BoujeeEnjinia1701/gridbench/cad/drawings/GBN-DWG-001.pdf

CONCEPT, NOT FOR FABRICATION | GridBench · github.com/BoujeeEnjinia1701/gridbench

FRONT VIEW
Scale 1:20; looking at the front (along +Y)

TOP VIEW
Scale 1:20; looking down (along -Z)

RIGHT VIEW
Scale 1:20; looking at the right side (along -X)

1200

600 1262

DETAIL A: TILE
Top view, scale 1:5

DETAIL A NOTES
Holes continue the field grid 4 fixing holes, 7 mm, C'bore 11 Tile 12.7 thick on 5.3 packers

FLOOR

1,090 FEET

14 BALLAST, 2 SLABS

825 | 300

6 PRECISION TILE, FLUSH

4 PLYWOOD FIELD, 25 GRID

122 LIGHT-DUTY RINGS (RED)

12.5

25

9 x 8 H7, 100 PITCH

144 x M6

ISOMETRIC VIEW
Not to scale; worktop holes shown as a representative patch; seen from the front right and above, about 30 deg elevation

MAIN DIMENSIONS AND INTERFACES (MM)
Worktop 1,200 x 600 x 18 birch ply, top at 900 ±15
Grid 25 pitch, first hole 12.5 from each edge; 1,152 positions
Field: 756 x 6.6 plain; 252 M6 on the 50 sub-grid: 130 tee nuts from below, 122 screw-in over frame Tile 300 x 300 x 12.7, left edge 825 from the worktop's left edge
Feet at 1,090 x 490 centers, rubber pads, in M10 T-nuts; legs 70 square
Aprons 45 x 120; cross rails 45 x 70 at X -300, 0, 247.5, 502.5
Clamp 1.6 N m max; 0.92 N m at the 122 red-ringed light-duty positions; round + diamond pin Aprons and low rails butt between the legs: 2 M8 bolts and cross dowels per end
Worktop on 9 steel angle brackets; tile on 4 M6 x 20 screws into rail inserts
Ballast 2 x 12.9 kg slabs on a shelf screwed to the low rails (8 screws)
Third-angle; front view from -Y; origin at worktop center
REV | DESCRIPTION | DATE | BY
P1 | Preliminary GA for TRL 3 (from cad/src/model.py) | 2026-09-25 | AC
P2 | Recommendations accepted (DDR-002): 45 x 120 aprons, tee nuts, rubber feet | 2026-09-25 | AC
P3 | Layout and labels tidied | 2026-09-25 | AC
P4 | Design for construction (DDR-003): bolted joints, brackets, tile fixing | 2026-10-01 | AC
P5 | Light-duty rings at the screw-in positions; shelf screwed to the low rails | 2026-10-02 | AC
GRIDBENCH | github.com/BoujeeEnjinia1701/gridbench

## General arrangement

DRAWING NO.
GBN-DWG-001

REV
P5

SHEET
1 of 1

SIZE

## ANSI B

SCALE
1:20

UNITS
mm
PROJECTION | DATE
2026-10-02

DRAWN
Amish Chadha

MATERIAL / NOTES
Softwood frame, birch plywood top, cast aluminum tile; bought-in parts per bom/bom.csv. PRELIMINARY, NOT FOR FABRICATION
Licensed CERN-OHL-S-2.0 · Design Molecule Lab · designmolecule.com | Generated from cad/src; do not edit by hand
