BoujeeEnjinia1701/gridbench/cad/drawings/GBN-DWG-104.pdf

### BUILD PLAN SKETCH, PLAN NOT YET BUILT GridBench · github.com/BoujeeEnjinia1701/gridbench

FRONT VIEW
Scale 1:10; looking at the front (along +Y)

TOP VIEW
Scale 1:10; looking down (along -Z)

RIGHT VIEW
Scale 1:10; looking at the right side (along -X)

70

45 1020

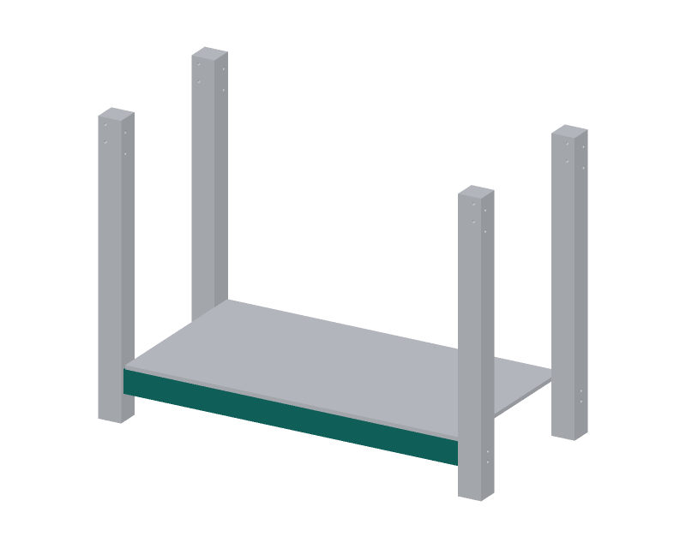
[picture p6: figure]

WHERE IT GOES
This part in colour, its neighbours in grey

HOW TO MAKE IT AND HOW IT FITS
Make two. Cut 45 x 70 mm softwood to 1,020 mm, ends square.
In each end: two 9 mm holes along the length, 52 mm deep, centred in the thickness, 20 and 50 mm up from the lower edge.
In the inside face: two 10 mm cross dowel holes 30 mm deep, 40 mm from the end, at the same heights.
Fit: butts between the legs on their centre line, 105 mm above the floor (80 mm above the foot of the leg); two M8 x 120 bolts and cross dowels at each end. The shelf rests on its top face and is screwed down into it at four points: 3 mm pilot holes, 20 mm deep, drilled through the shelf in step 7.
Check: same length as the long aprons within 0.5 mm.
REV | DESCRIPTION | DATE | BY
P1 | Making sketch for the prototype build plan | 2026-10-01 | AC
P2 | Shelf screwed down into the top face | 2026-10-02 | AC
GRIDBENCH | github.com/BoujeeEnjinia1701/gridbench

## GridBench low rail (make 2): making sketch

DRAWING NO.
GBN-DWG-104

REV
P2

SHEET
1 of 1

SIZE

## ANSI B

SCALE
1:10

UNITS
mm
PROJECTION | DATE
2026-10-02

DRAWN
Amish Chadha

MATERIAL / NOTES
Sawn softwood 45 x 70 mm, C16 or better
Licensed CERN-OHL-S-2.0 · Design Molecule Lab · designmolecule.com | Generated from cad/src; do not edit by hand
