BoujeeEnjinia1701/gridbench/cad/drawings/GBN-DWG-107.pdf

### BUILD PLAN SKETCH, PLAN NOT YET BUILT GridBench · github.com/BoujeeEnjinia1701/gridbench

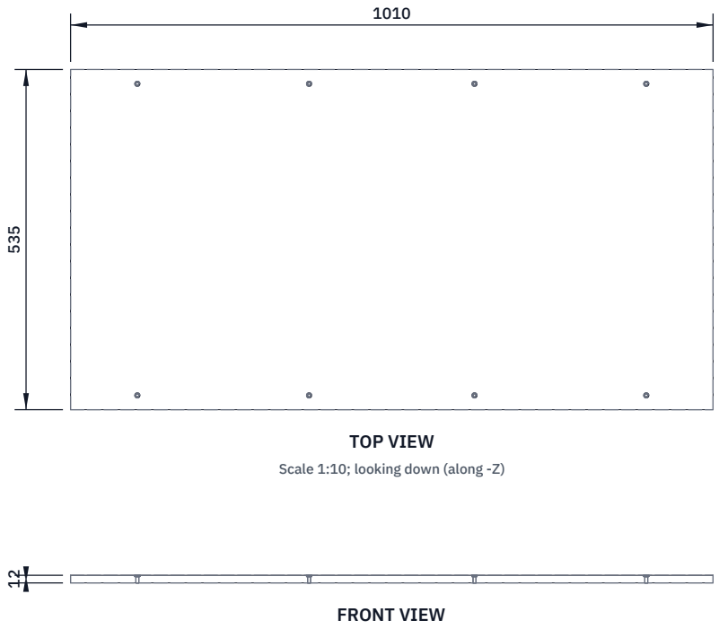
[picture p7: figure]
FRONT VIEW; TOP VIEW; Scale 1:10; looking down (along -Z)

Scale 1:10; looking at the front (along +Y)

RIGHT VIEW
Scale 1:10; looking at the right side (along -X)

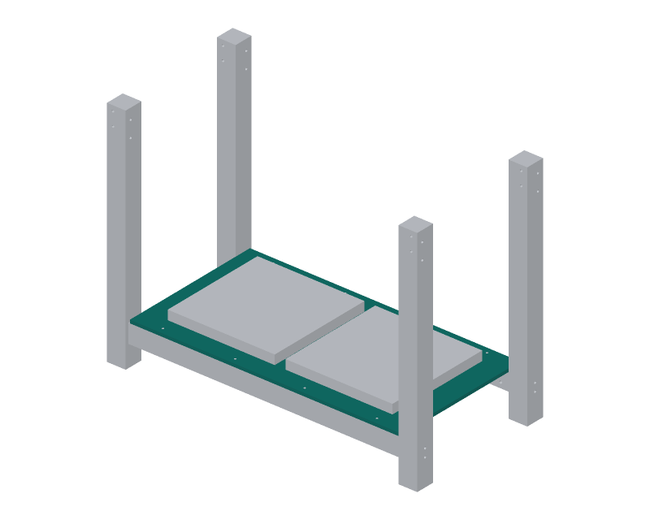
[picture p8: figure]

WHERE IT GOES
This part in colour, its neighbours in grey

HOW TO MAKE IT AND HOW IT FITS
Cut 12 mm plywood to 1,010 x 535 mm, square.
Round the corners about 5 mm and sand the edges.
Drill eight 4.5 mm holes, countersunk for an 8 mm head: four along each long edge, 22.5 mm in from the edge, at 105, 375, 635 and 905 mm from the left end.
Fit: rests on the top faces of the two low rails, flush with their outside faces, 5 mm clear of the legs at each end. It is slid in from the front, above the front low rail, then lowered and held down by eight 4 x 30 mm countersunk wood screws into the rails. It carries the two ballast slabs, side by side, 40 mm apart. Check: it lies flat on both rails and does not touch a leg.
REV | DESCRIPTION | DATE | BY
P1 | Making sketch for the prototype build plan | 2026-10-01 | AC
P2 | Eight countersunk screw holes; shelf screwed to the low rails | 2026-10-02 | AC
GRIDBENCH | github.com/BoujeeEnjinia1701/gridbench

## GridBench shelf: making sketch

DRAWING NO.
GBN-DWG-107

REV
P2

SHEET
1 of 1

SIZE

## ANSI B

SCALE
1:10

UNITS
mm
PROJECTION | DATE
2026-10-02

DRAWN
Amish Chadha

MATERIAL / NOTES
Plywood 12 mm
Licensed CERN-OHL-S-2.0 · Design Molecule Lab · designmolecule.com | Generated from cad/src; do not edit by hand
