BoujeeEnjinia1701/gridbench/cad/drawings/GBN-DWG-108.pdf

### BUILD PLAN SKETCH, PLAN NOT YET BUILT GridBench · github.com/BoujeeEnjinia1701/gridbench

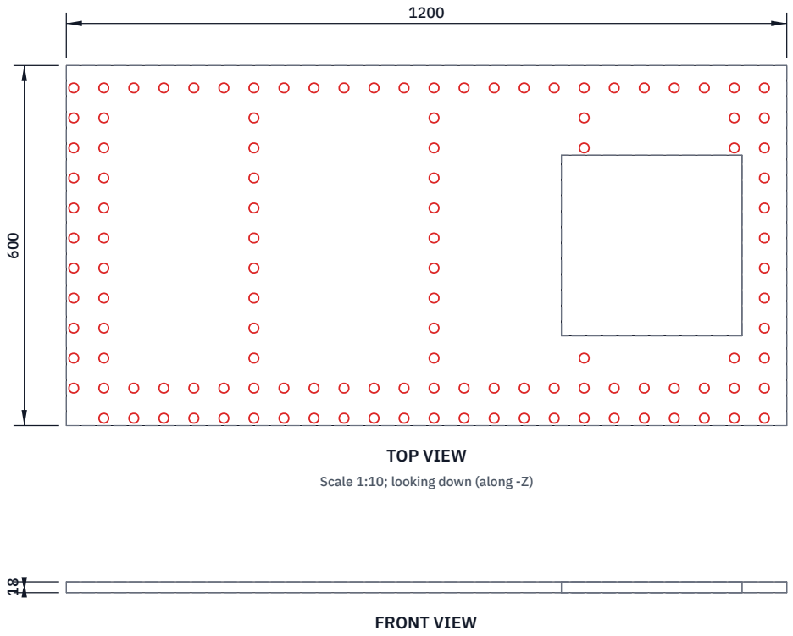
[picture p9: figure]
FRONT VIEW; TOP VIEW; Scale 1:10; looking down (along -Z)

Scale 1:10; looking at the front (along +Y)

RIGHT VIEW
Scale 1:10; looking at the right side (along -X)

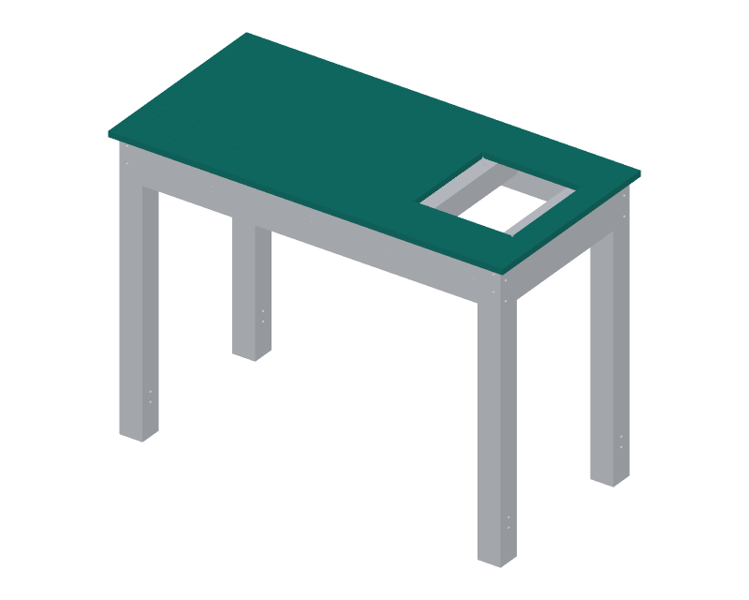
[picture p10: figure]

WHERE IT GOES
This part in colour, its neighbours in grey

HOW TO MAKE IT AND HOW IT FITS
Cut 18 mm birch plywood to 1,200 x 600 mm, square within 0.5 mm. Holes (shown on the hole layout, not here): 1,008 on a 25 mm grid, first centres 12.5 mm from the left and front edges; 756 plain 6.6 mm,
130 at 8.0 mm for tee nuts, 122 at 8.5 mm for screw-in inserts.
Drill on a shared CNC router, or with a printed drilling template
indexed from the left and front edges, never from the last hole.
Tile pocket: 301 x 301 mm right through, 824.5 to 1,125.5 mm from the left edge and 149.5 to 450.5 mm from the front edge. Drill an 8 mm relief hole on each corner first, then jigsaw and rout to the line.
Round all edges 1 mm; seal both faces with a thin finish.
Red rings (top view): paint a ring about 16 mm across round each of the 122 screw-in positions in a contrasting colour. They are light duty: a clamp there is tightened to 0.92 N m at most.
Fit: on the aprons and rails, held by nine steel brackets from below. Check: corner to corner diagonals equal within 1 mm.
REV | DESCRIPTION | DATE | BY
P1 | Making sketch for the prototype build plan | 2026-10-01 | AC
P2 | Red rings at the 122 light-duty screw-in positions | 2026-10-02 | AC
GRIDBENCH | github.com/BoujeeEnjinia1701/gridbench

## GridBench worktop: making sketch

DRAWING NO.
GBN-DWG-108

REV
P2

SHEET
1 of 1

SIZE

## ANSI B

SCALE
1:10

UNITS
mm
PROJECTION | DATE
2026-10-02

DRAWN
Amish Chadha

MATERIAL / NOTES
Birch plywood 18 mm, one 1,200 x 600 mm panel
Licensed CERN-OHL-S-2.0 · Design Molecule Lab · designmolecule.com | Generated from cad/src; do not edit by hand
