BoujeeEnjinia1701/gridbench/cad/drawings/GBN-DWG-101.pdf

### BUILD PLAN SKETCH, PLAN NOT YET BUILT GridBench · github.com/BoujeeEnjinia1701/gridbench

FRONT VIEW
Scale 1:10; looking at the front (along +Y)

TOP VIEW
Scale 1:10; looking down (along -Z)

RIGHT VIEW
Scale 1:10; looking at the right side (along -X)

70

70 857

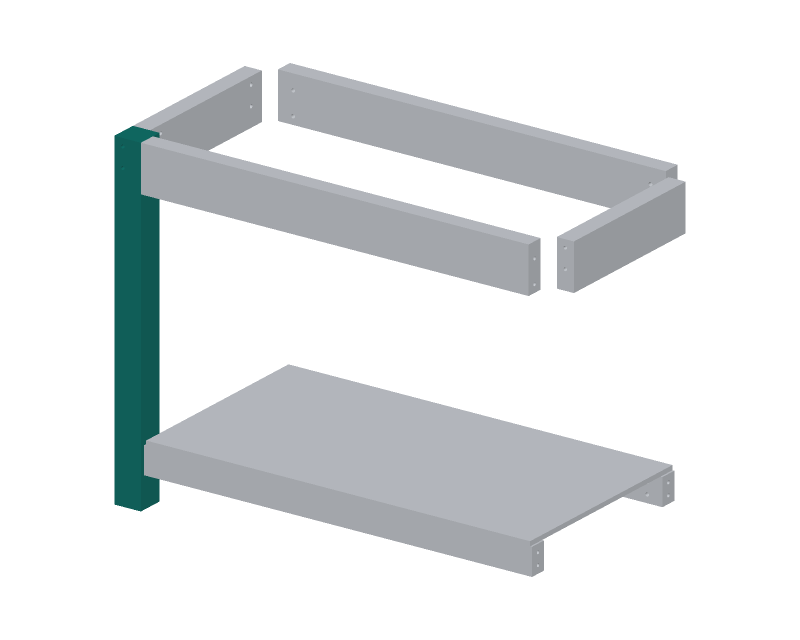
[picture p58: figure]

WHERE IT GOES
This part in colour, its neighbours in grey

HOW TO MAKE IT AND HOW IT FITS
Make four. Cut 70 x 70 mm softwood to 857 mm, square both ends. Each leg has an outside corner, where its end face (toward the end of the bench) meets its side face (toward the front or back).
End face: two 9 mm holes 12.5 mm from the centre toward the outside corner, 40 and 100 mm down from the top (long apron); two 9 mm holes on the centre line, 100 and 130 mm up from the foot (low rail). Side face: two 9 mm holes 12.5 mm from the centre toward the outside corner, 20 and 70 mm down from the top (end apron).
Drill all six square to the face, right through, in a drill stand.
Foot: bore 12 mm, 60 deep, on the centre; tap in the M10 T-nut.
Round or chamfer every outside edge about 2 mm.
Check: a 9 mm rod passes each hole square; the leg stands upright.
REV | DESCRIPTION | DATE | BY
P1 | Making sketch for the prototype build plan | 2026-10-01 | AC
GRIDBENCH | github.com/BoujeeEnjinia1701/gridbench

## GridBench leg (make 4): making sketch

DRAWING NO.
GBN-DWG-101

REV
P1

SHEET
1 of 1

SIZE

## ANSI B

SCALE
1:10

UNITS
mm
PROJECTION | DATE
2026-10-01

DRAWN
Amish Chadha

MATERIAL / NOTES
Sawn softwood 70 x 70 mm, C16 or better
Licensed CERN-OHL-S-2.0 · Design Molecule Lab · designmolecule.com | Generated from cad/src; do not edit by hand
