BoujeeEnjinia1701/gridbench/cad/drawings/GBN-DWG-102.pdf

### BUILD PLAN SKETCH, PLAN NOT YET BUILT GridBench · github.com/BoujeeEnjinia1701/gridbench

FRONT VIEW
Scale 1:5; looking at the front (along +Y)

TOP VIEW
Scale 1:5; looking down (along -Z)

RIGHT VIEW
Scale 1:5; looking at the right side (along -X)

45

420 120

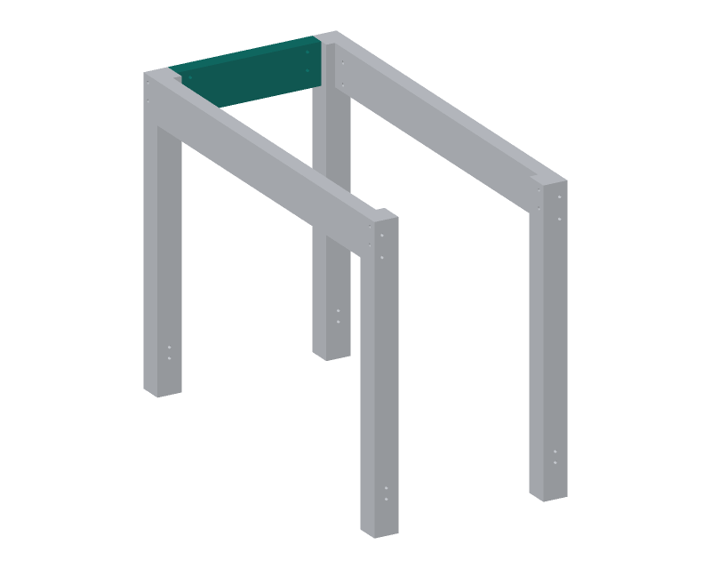
[picture p59: figure]

WHERE IT GOES
This part in colour, its neighbours in grey

HOW TO MAKE IT AND HOW IT FITS
Make two. Cut 45 x 120 mm softwood to 420 mm, ends square.
In each end: two 9 mm holes along the length, 52 mm deep, centred in the 45 mm thickness, 50 and 100 mm up from the lower edge.
In the inside face: two 10 mm holes 30 mm deep, 40 mm from the end, at the same heights. They meet the end holes; the cross dowels (barrel nuts) go in here and the bolts screw into them.
Fit: butts between two legs, flush with their tops and outside faces, held by two M8 x 120 bolts through the leg into the cross dowels. Check: an M8 bolt pushed into an end hole shows through the cross dowel hole; the ends are square to the faces.
REV | DESCRIPTION | DATE | BY
P1 | Making sketch for the prototype build plan | 2026-10-01 | AC
GRIDBENCH | github.com/BoujeeEnjinia1701/gridbench

## GridBench end apron (make 2): making sketch

DRAWING NO.
GBN-DWG-102

REV
P1

SHEET
1 of 1

SIZE

## ANSI B

SCALE
1:5

UNITS
mm
PROJECTION | DATE
2026-10-01

DRAWN
Amish Chadha

MATERIAL / NOTES
Sawn softwood 45 x 120 mm, C16 or better
Licensed CERN-OHL-S-2.0 · Design Molecule Lab · designmolecule.com | Generated from cad/src; do not edit by hand
