BoujeeEnjinia1701/gridbench/cad/drawings/GBN-DWG-103.pdf

### BUILD PLAN SKETCH, PLAN NOT YET BUILT GridBench · github.com/BoujeeEnjinia1701/gridbench

FRONT VIEW
Scale 1:10; looking at the front (along +Y)

TOP VIEW
Scale 1:10; looking down (along -Z)

RIGHT VIEW
Scale 1:10; looking at the right side (along -X)

120

45 1020

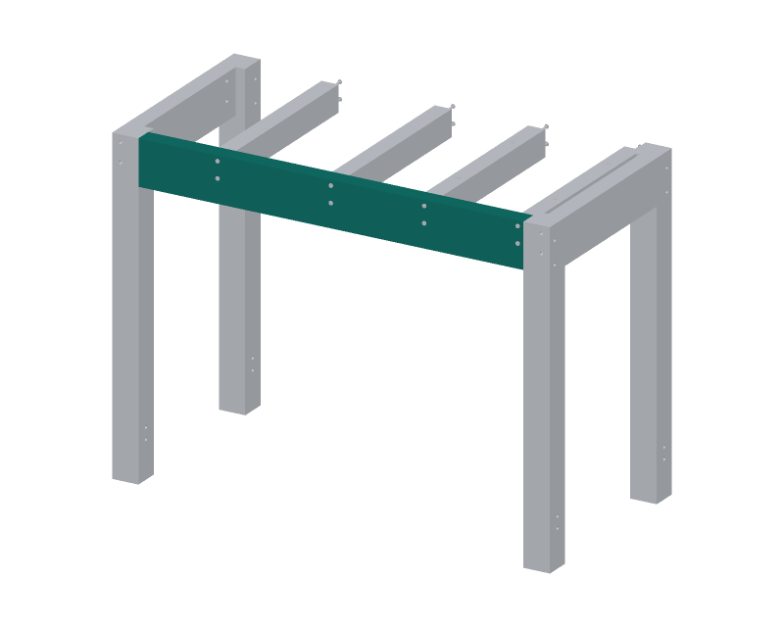
[picture p60: figure]

WHERE IT GOES
This part in colour, its neighbours in grey

HOW TO MAKE IT AND HOW IT FITS
Make two. Cut 45 x 120 mm softwood to 1,020 mm, ends square.
In each end: two 9 mm holes along the length, 52 mm deep, centred in the thickness, 20 and 80 mm up from the lower edge.
In the inside face: two 10 mm cross dowel holes 30 mm deep, 40 mm from the end, at the same heights.
Cross rail screws: 4 mm pilot holes right through, 63 and 106 mm up from the lower edge, at 210, 510, 757.5 and 1,005 mm from the left end. Fit: butts between the legs, flush with their tops and outside faces,
on two M8 x 120 bolts and cross dowels at each end.
The cross rails butt against the inside face; brackets hold the top. Check: the two aprons are the same length within 0.5 mm.
REV | DESCRIPTION | DATE | BY
P1 | Making sketch for the prototype build plan | 2026-10-01 | AC
GRIDBENCH | github.com/BoujeeEnjinia1701/gridbench

## GridBench long apron (make 2): making sketch

DRAWING NO.
GBN-DWG-103

REV
P1

SHEET
1 of 1

SIZE

## ANSI B

SCALE
1:10

UNITS
mm
PROJECTION | DATE
2026-10-01

DRAWN
Amish Chadha

MATERIAL / NOTES
Sawn softwood 45 x 120 mm, C16 or better
Licensed CERN-OHL-S-2.0 · Design Molecule Lab · designmolecule.com | Generated from cad/src; do not edit by hand
