BoujeeEnjinia1701/gridbench/cad/drawings/GBN-DWG-105.pdf

### BUILD PLAN SKETCH, PLAN NOT YET BUILT GridBench · github.com/BoujeeEnjinia1701/gridbench

FRONT VIEW
Scale 1:5; looking at the front (along +Y)

TOP VIEW
Scale 1:5; looking down (along -Z)

RIGHT VIEW
Scale 1:5; looking at the right side (along -X)

45

470 70

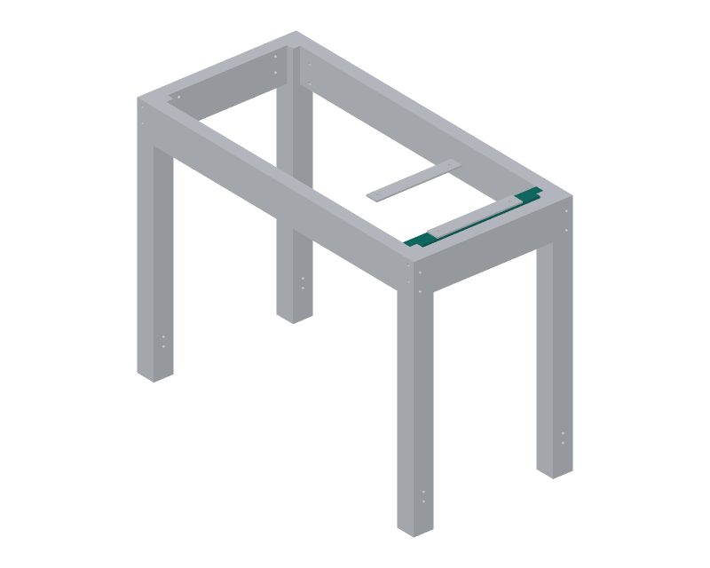
[picture p61: figure]

WHERE IT GOES
This part in colour, its neighbours in grey

HOW TO MAKE IT AND HOW IT FITS
Make four. Cut 45 x 70 mm softwood to 470 mm, ends square. Drawn: the rail nearest the right-hand legs. Saw a notch 15 mm wide (along the bench) by 25 mm long out of each end, full height, on
the side toward the legs, so the rail clears their corners.
The other three rails are plain.
Ends: two 4 mm pilot holes 40 mm deep, 13 and 56 mm up from the lower edge (in the unnotched 30 mm of the notched rail).
Fit: tops flush with the aprons; centres 210, 510, 757.5 and 1,012.5 mm from the inside face of the left legs. Two 6 x 100 mm structural
screws through the apron into each end.
The two 8.5 mm holes shown (tile rails only) are drilled in step 10. Check: each rail drops between the aprons without forcing.
REV | DESCRIPTION | DATE | BY
P1 | Making sketch for the prototype build plan | 2026-10-01 | AC
GRIDBENCH | github.com/BoujeeEnjinia1701/gridbench

## GridBench cross rail (make 4; one notched): making sketch

DRAWING NO.
GBN-DWG-105

REV
P1

SHEET
1 of 1

SIZE

## ANSI B

SCALE
1:5

UNITS
mm
PROJECTION | DATE
2026-10-01

DRAWN
Amish Chadha

MATERIAL / NOTES
Sawn softwood 45 x 70 mm, C16 or better
Licensed CERN-OHL-S-2.0 · Design Molecule Lab · designmolecule.com | Generated from cad/src; do not edit by hand
