BoujeeEnjinia1701/gridbench/cad/drawings/GBN-DWG-106.pdf

### BUILD PLAN SKETCH, PLAN NOT YET BUILT GridBench · github.com/BoujeeEnjinia1701/gridbench

FRONT VIEW
Scale 1:5; looking at the front (along +Y)

TOP VIEW
Scale 1:5; looking down (along -Z)

RIGHT VIEW
Scale 1:5; looking at the right side (along -X)

45

300 5

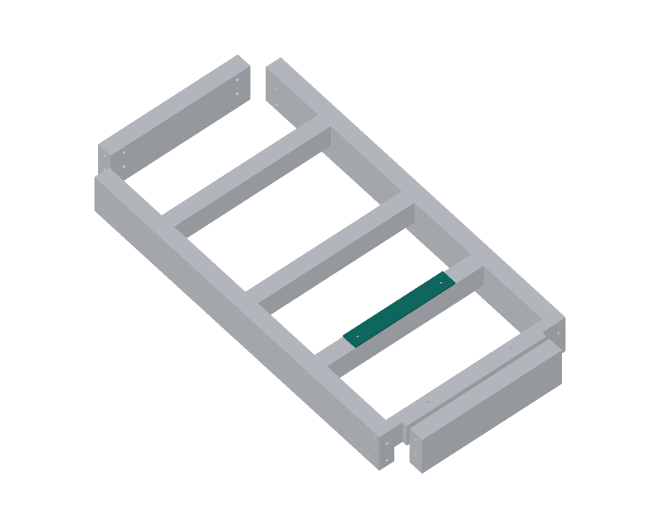
[picture p62: figure]

WHERE IT GOES
This part in colour, its neighbours in grey

HOW TO MAKE IT AND HOW IT FITS
Make two. Hardwood strip 45 wide, 300 long, planed to 5.3 mm. The right thickness is 18 mm (the worktop) less the tile's real thickness: measure the tile and the worktop first and plane to suit, so the tile sits flush with the plywood.
Fit: glued to the top of each of the two tile rails, centred on the rail, running front to back under the tile pocket.
Two 8.5 mm insert holes go through it in step 10, 125 mm each side of the centre.
Check: both packers the same thickness within 0.05 mm.
REV | DESCRIPTION | DATE | BY
P1 | Making sketch for the prototype build plan | 2026-10-01 | AC
GRIDBENCH | github.com/BoujeeEnjinia1701/gridbench

## GridBench packer under the tile (make 2): making sketch

DRAWING NO.
GBN-DWG-106

REV
P1

SHEET
1 of 1

SIZE

## ANSI B

SCALE
1:5

UNITS
mm
PROJECTION | DATE
2026-10-01

DRAWN
Amish Chadha

MATERIAL / NOTES
Hardwood strip 45 x 6 mm, planed
Licensed CERN-OHL-S-2.0 · Design Molecule Lab · designmolecule.com | Generated from cad/src; do not edit by hand
