BoujeeEnjinia1701/gridbench/cad/drawings/GBN-DWG-109.pdf

### BUILD PLAN SKETCH, PLAN NOT YET BUILT GridBench · github.com/BoujeeEnjinia1701/gridbench

FRONT VIEW
Scale 1:5; looking at the front (along +Y)

TOP VIEW
Scale 1:5; looking down (along -Z)

RIGHT VIEW
Scale 1:5; looking at the right side (along -X)

300

300 13

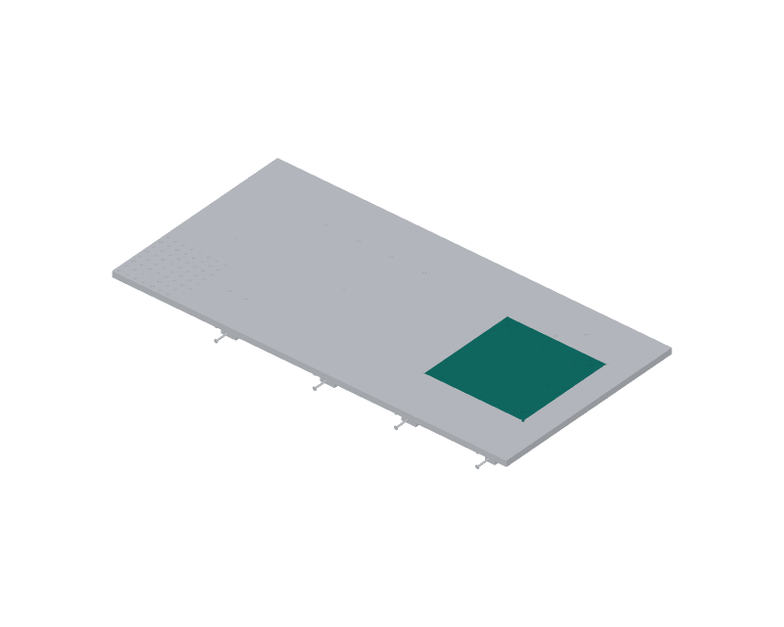
[picture p63: figure]

WHERE IT GOES
This part in colour, its neighbours in grey

HOW TO MAKE IT AND HOW IT FITS
Cast tooling plate 300 x 300 x 12.7 mm, edges square; chamfer 0.5 mm. Measure from the left and front edges. 144 M6 holes on a 25 mm grid, first centres 12.5 mm in: drill 5.0 mm through in a drilling jig,
then tap M6 with a spiral-point tap held square in a tapping guide.
Nine dowel bores at 50, 150 and 250 mm both ways (centres of grid squares): drill 7.8 mm, then ream 8 mm H7 through.
Four fixing holes 7 mm, 22.5 mm in from the left and right edges and 25 mm in from the front and back edges; counterbore 11 mm, 6.5 mm deep, from the top, for M6 x 20 cap screws.
Deburr; stone the top flat. Mark the top face and the front edge. Fit: flush in the worktop pocket, 0.5 mm gap round it, on the packers; four screws into inserts in the two tile rails.
Check: an 8 mm h6 pin slides into every bore; holes on pitch ±0.05.
REV | DESCRIPTION | DATE | BY
P1 | Making sketch for the prototype build plan | 2026-10-01 | AC
GRIDBENCH | github.com/BoujeeEnjinia1701/gridbench

## GridBench precision tile: making sketch

DRAWING NO.
GBN-DWG-109

REV
P1

SHEET
1 of 1

SIZE

## ANSI B

SCALE
1:5

UNITS
mm
PROJECTION | DATE
2026-10-01

DRAWN
Amish Chadha

MATERIAL / NOTES
Cast aluminium tooling plate 300 x 300 x 12.7 mm
Licensed CERN-OHL-S-2.0 · Design Molecule Lab · designmolecule.com | Generated from cad/src; do not edit by hand
