BoujeeEnjinia1701/gridbench/cad/drawings/GBN-DWG-110.pdf

### BUILD PLAN SKETCH, PLAN NOT YET BUILT GridBench · github.com/BoujeeEnjinia1701/gridbench

FRONT VIEW
Scale 1:1; looking at the front (along +Y)

TOP VIEW
Scale 1:1; looking down (along -Z)

RIGHT VIEW
Scale 1:1; looking at the right side (along -X)

70

24 70

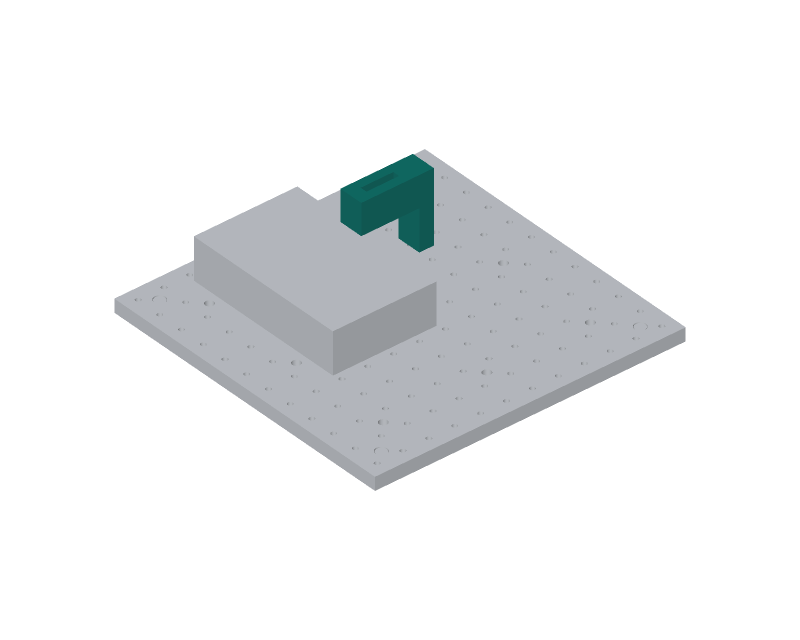
[picture p64: figure]

WHERE IT GOES
This part in colour, its neighbours in grey

HOW TO MAKE IT AND HOW IT FITS
Print four in PETG lying on a side face, so the layers run along the clamp: 6 walls, 40 % infill, about 50 g each.
Body 70 long, 24 wide, 30 deep. Slot 6.6 mm wide, 31.5 mm long, its centre 7 mm from the middle toward the toe end.
Heel at the other end, 14 mm long, as tall as the work (40 mm here). Fit: an M6 x 80 cap screw with a printed knob passes through the slot into a threaded hole; the toe presses the work, the heel
stands on the table. Slide the body so the screw is nearer the toe. Mark 1.6 N m MAX on the top: never tighten past it.
Check: no cracks or gaps between layers at the slot ends.
REV | DESCRIPTION | DATE | BY
P1 | Making sketch for the prototype build plan | 2026-10-01 | AC
GRIDBENCH | github.com/BoujeeEnjinia1701/gridbench

## GridBench printed toe clamp (make 4): making sketch

DRAWING NO.
GBN-DWG-110

REV
P1

SHEET
1 of 1

SIZE

## ANSI B

SCALE
1:1

UNITS
mm
PROJECTION | DATE
2026-10-01

DRAWN
Amish Chadha

MATERIAL / NOTES
PETG, 3D printed, 6 walls, 40 % infill
Licensed CERN-OHL-S-2.0 · Design Molecule Lab · designmolecule.com | Generated from cad/src; do not edit by hand
