BoujeeEnjinia1701/gridbench/cad/drawings/GBN-DWG-111.pdf

### BUILD PLAN SKETCH, PLAN NOT YET BUILT GridBench · github.com/BoujeeEnjinia1701/gridbench

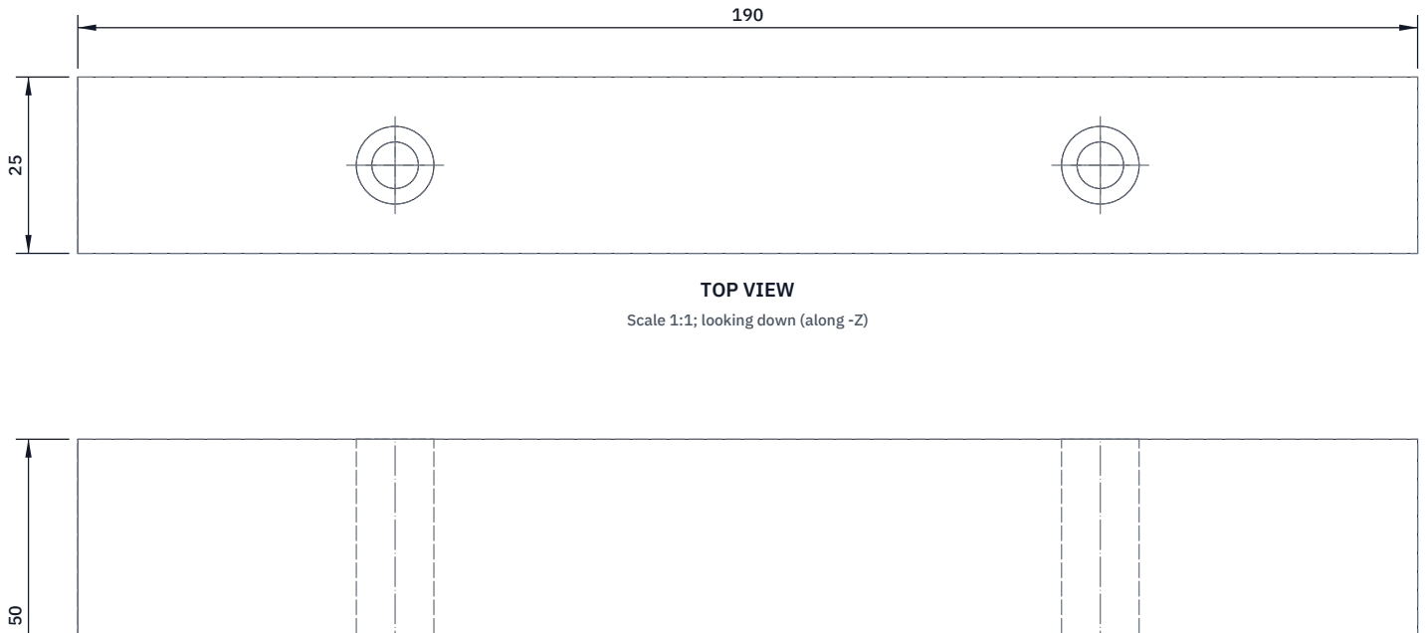
[picture p65: figure]
TOP VIEW; Scale 1:1; looking down (along -Z)

FRONT VIEW
Scale 1:1; looking at the front (along +Y)

RIGHT VIEW
Scale 1:1; looking at the right side (along -X)

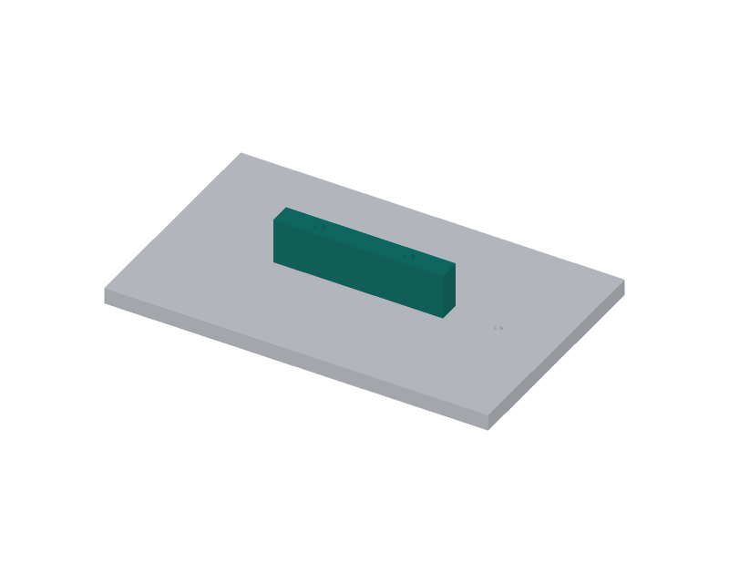
[picture p66: figure]

WHERE IT GOES
This part in colour, its neighbours in grey

HOW TO MAKE IT AND HOW IT FITS
Print two in PETG, lying on a 190 x 50 mm face: 190 long, 25 wide, 50 tall. Every part fits a 200 x 200 mm bed.
Two 6.6 mm holes top to bottom, 50 mm each side of the centre (100 apart, on the threaded 50 mm sub-grid).
Counterbore each 11 mm from the top down to 12 mm above the base, so an M6 x 30 cap screw reaches the thread below the worktop.
Fit: two M6 x 30 cap screws into threaded grid positions; the two segments stand end to end with a 10 mm gap.
Check: the front face is square to the base (engineer's square).
REV | DESCRIPTION | DATE | BY
P1 | Making sketch for the prototype build plan | 2026-10-01 | AC
GRIDBENCH | github.com/BoujeeEnjinia1701/gridbench

## GridBench fence segment (make 2): making sketch

DRAWING NO.
GBN-DWG-111

REV
P1

SHEET
1 of 1

SIZE

## ANSI B

SCALE
1:1

UNITS
mm
PROJECTION | DATE
2026-10-01

DRAWN
Amish Chadha

MATERIAL / NOTES
PETG, 3D printed
Licensed CERN-OHL-S-2.0 · Design Molecule Lab · designmolecule.com | Generated from cad/src; do not edit by hand
