BoujeeEnjinia1701/gridbench/cad/drawings/GBN-DWG-114.pdf

### BUILD PLAN SKETCH, PLAN NOT YET BUILT GridBench · github.com/BoujeeEnjinia1701/gridbench

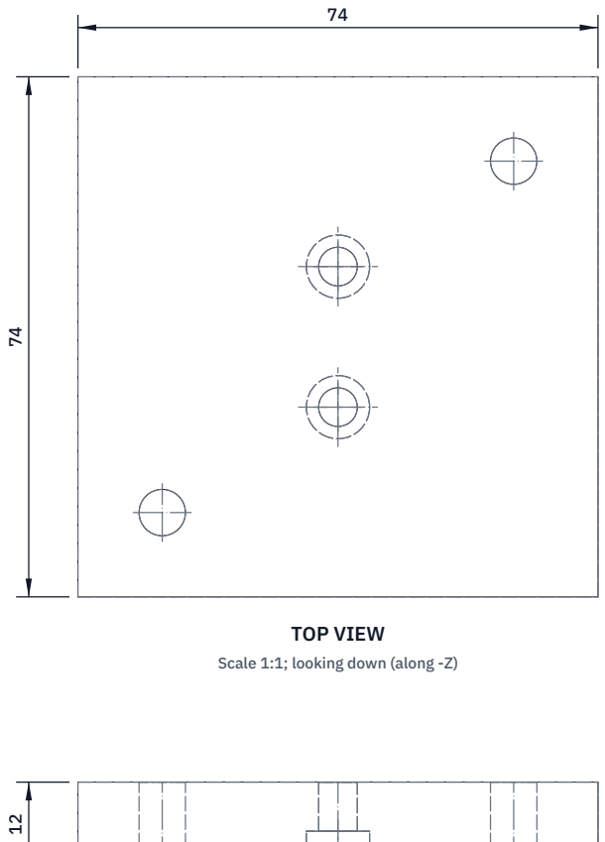
[picture p67: figure]
TOP VIEW; Scale 1:1; looking down (along -Z)

FRONT VIEW
Scale 1:1; looking at the front (along +Y)

RIGHT VIEW
Scale 1:1; looking at the right side (along -X)

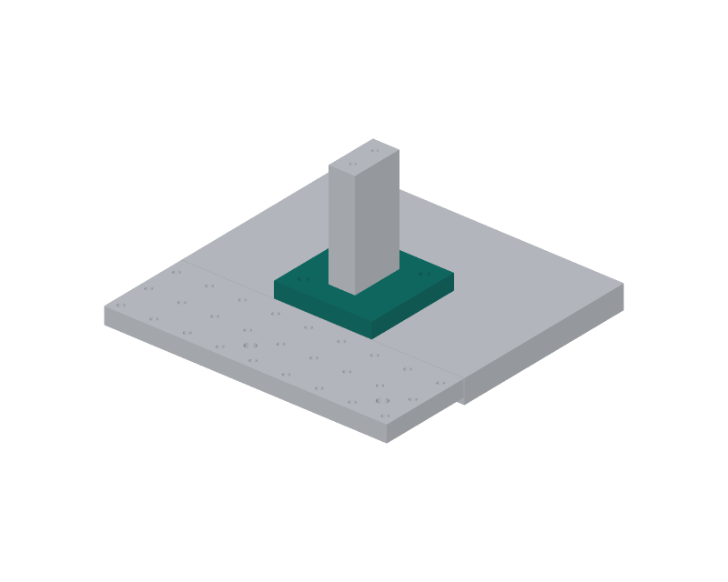
[picture p68: figure]

WHERE IT GOES
This part in colour, its neighbours in grey

HOW TO MAKE IT AND HOW IT FITS
Print flat in PETG at 100 % infill: 74 x 74 x 12 mm.
Two 6.6 mm holes at opposite corners, 25 mm from the centre both ways (on the threaded 50 mm sub-grid), for M6 x 30 cap screws. Two 5.5 mm holes on the centre line, 10 mm each side of the centre, counterbored 9 mm, 5 mm deep, from the underside, for the M5 x 20 screws that go up into the extrusion.
Fit: the extrusion stands on its top face, its 40 mm side front to back; the foot screws down onto any two threaded grid positions. Check: the extrusion stands square to the foot.
REV | DESCRIPTION | DATE | BY
P1 | Making sketch for the prototype build plan | 2026-10-01 | AC
GRIDBENCH | github.com/BoujeeEnjinia1701/gridbench

## GridBench instrument post foot: making sketch

DRAWING NO.
GBN-DWG-114

REV
P1

SHEET
1 of 1

SIZE

## ANSI B

SCALE
1:1

UNITS
mm
PROJECTION | DATE
2026-10-01

DRAWN
Amish Chadha

MATERIAL / NOTES
PETG, 3D printed, 100 % infill
Licensed CERN-OHL-S-2.0 · Design Molecule Lab · designmolecule.com | Generated from cad/src; do not edit by hand
