BoujeeEnjinia1701/gridbench/cad/drawings/GBN-DWG-115.pdf

### BUILD PLAN SKETCH, PLAN NOT YET BUILT GridBench · github.com/BoujeeEnjinia1701/gridbench

FRONT VIEW
Scale 1:1; looking at the front (along +Y)

TOP VIEW
Scale 1:1; looking down (along -Z)

RIGHT VIEW
Scale 1:1; looking at the right side (along -X)

64

50 40

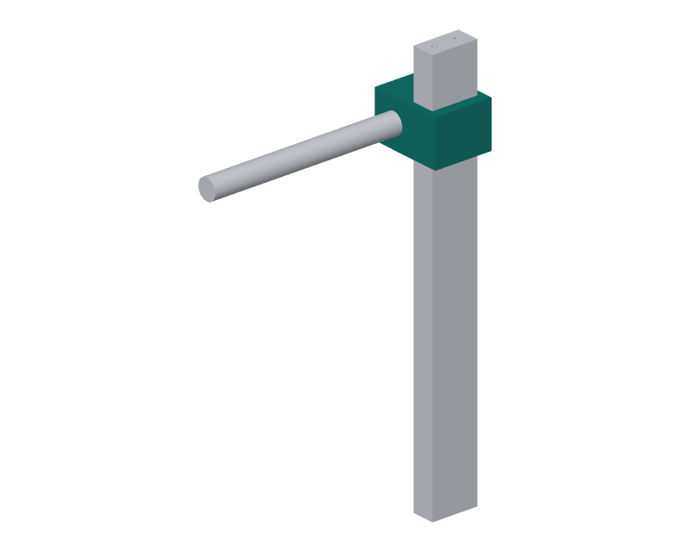
[picture p69: figure]

WHERE IT GOES
This part in colour, its neighbours in grey

HOW TO MAKE IT AND HOW IT FITS
Print in PETG at 100 % infill: 64 wide, 50 deep, 40 tall.
Slot 20.4 x 40.4 mm top to bottom for the post (0.2 mm clear each side), its centre 13 mm right of the block's centre.
Bore 18.4 mm front to back for the arm, 25 mm left of the post centre and half way up, so the arm passes beside the post. Print a hex pocket for an M6 nut and a 6.6 mm hole into the slot and into the bore, each locked by an M6 thumb screw.
Fit: slides on the post; the arm slides through the bore.
Check: slides freely when loose and does not move when locked.
REV | DESCRIPTION | DATE | BY
P1 | Making sketch for the prototype build plan | 2026-10-01 | AC
GRIDBENCH | github.com/BoujeeEnjinia1701/gridbench

## GridBench arm clamp (on the post): making sketch

DRAWING NO.
GBN-DWG-115

REV
P1

SHEET
1 of 1

SIZE

## ANSI B

SCALE
1:1

UNITS
mm
PROJECTION | DATE
2026-10-01

DRAWN
Amish Chadha

MATERIAL / NOTES
PETG, 3D printed, 100 % infill
Licensed CERN-OHL-S-2.0 · Design Molecule Lab · designmolecule.com | Generated from cad/src; do not edit by hand
