BoujeeEnjinia1701/gridbench/cad/drawings/GBN-DWG-116.pdf

### BUILD PLAN SKETCH, PLAN NOT YET BUILT GridBench · github.com/BoujeeEnjinia1701/gridbench

FRONT VIEW
Scale 1:1; looking at the front (along +Y)

TOP VIEW
Scale 1:1; looking down (along -Z)

RIGHT VIEW
Scale 1:1; looking at the right side (along -X)

30

50 30

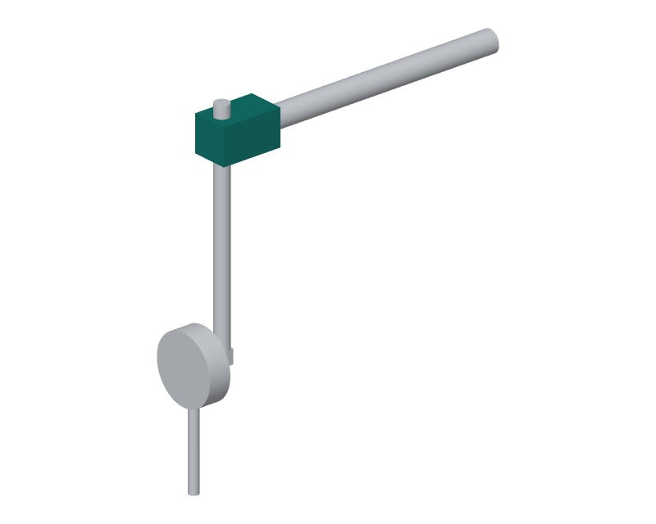
[picture p70: figure]

WHERE IT GOES
This part in colour, its neighbours in grey

HOW TO MAKE IT AND HOW IT FITS
Print in PETG at 100 % infill: 30 wide, 50 deep, 30 tall.
Arm bore 18.4 mm from the back face, 27 mm deep (blind).
Drop rod bore 12.4 mm top to bottom, its centre 14 mm in front of the block's centre, so it passes 6 mm in front of the arm's end. Hex pockets and 6.6 mm holes for two M6 thumb screws, one onto the arm and one onto the drop rod.
Fit: on the end of the arm; the 12 mm drop rod slides up and down in it and carries the dial indicator by its lug back.
Check: the drop rod stands upright when the arm is level.
REV | DESCRIPTION | DATE | BY
P1 | Making sketch for the prototype build plan | 2026-10-01 | AC
GRIDBENCH | github.com/BoujeeEnjinia1701/gridbench

## GridBench end clamp (arm to drop rod): making sketch

DRAWING NO.
GBN-DWG-116

REV
P1

SHEET
1 of 1

SIZE

## ANSI B

SCALE
1:1

UNITS
mm
PROJECTION | DATE
2026-10-01

DRAWN
Amish Chadha

MATERIAL / NOTES
PETG, 3D printed, 100 % infill
Licensed CERN-OHL-S-2.0 · Design Molecule Lab · designmolecule.com | Generated from cad/src; do not edit by hand
