BoujeeEnjinia1701/gridbench/cad/drawings/GBN-DWG-001.png

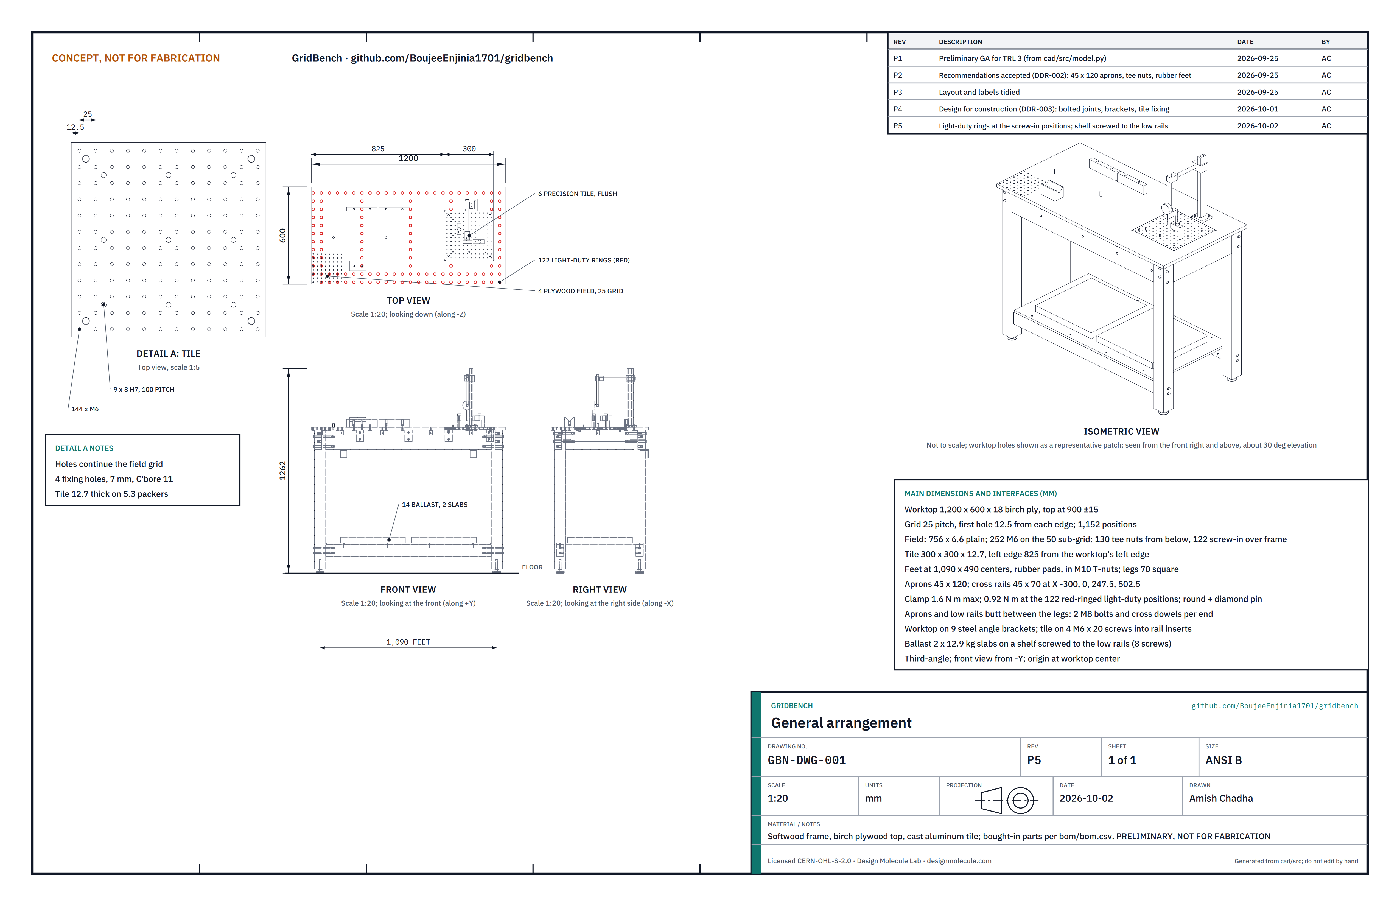
cad/drawings/GBN-DWG-001.png
