BoujeeEnjinia1701/gridbench/media/card.png

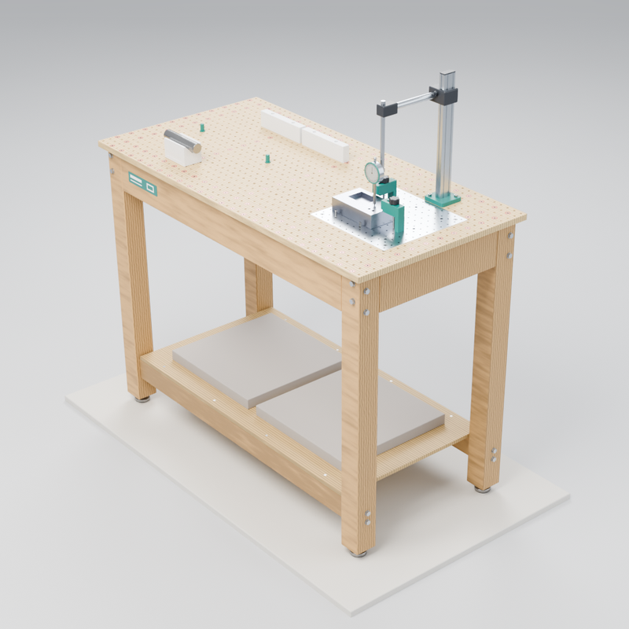
media/card.png
