BoujeeEnjinia1701/gridbench/media/render-detail.png

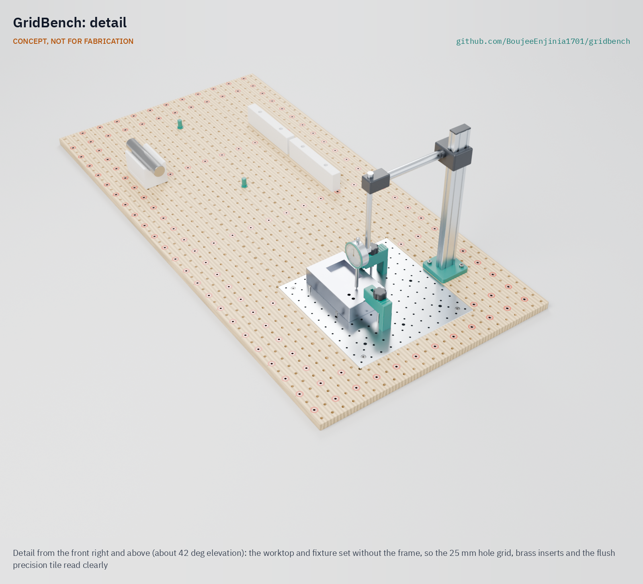
media/render-detail.png
