BoujeeEnjinia1701/gridbench/media/render-exploded.png

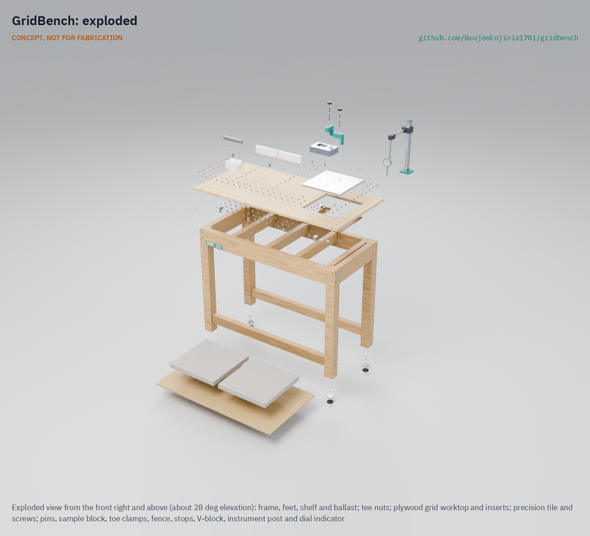
media/render-exploded.png
