BoujeeEnjinia1701/gridbench/media/social-preview.png

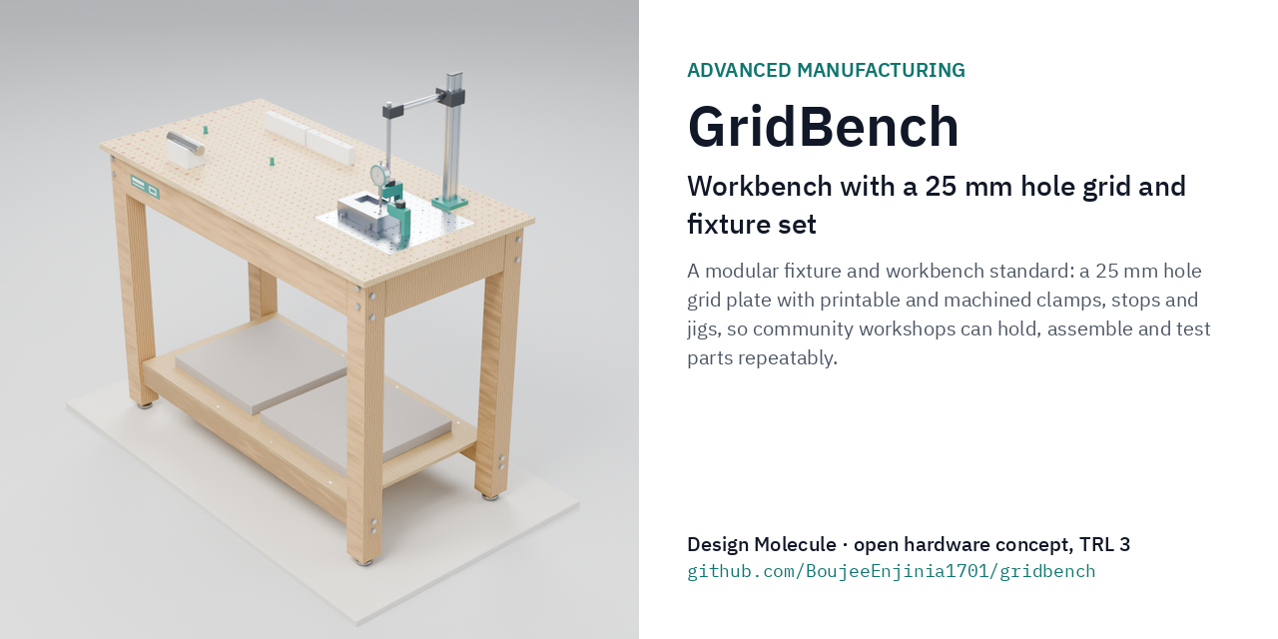
media/social-preview.png
