BoujeeEnjinia1701/gridbench/cad/drawings/GBN-DWG-112.pdf

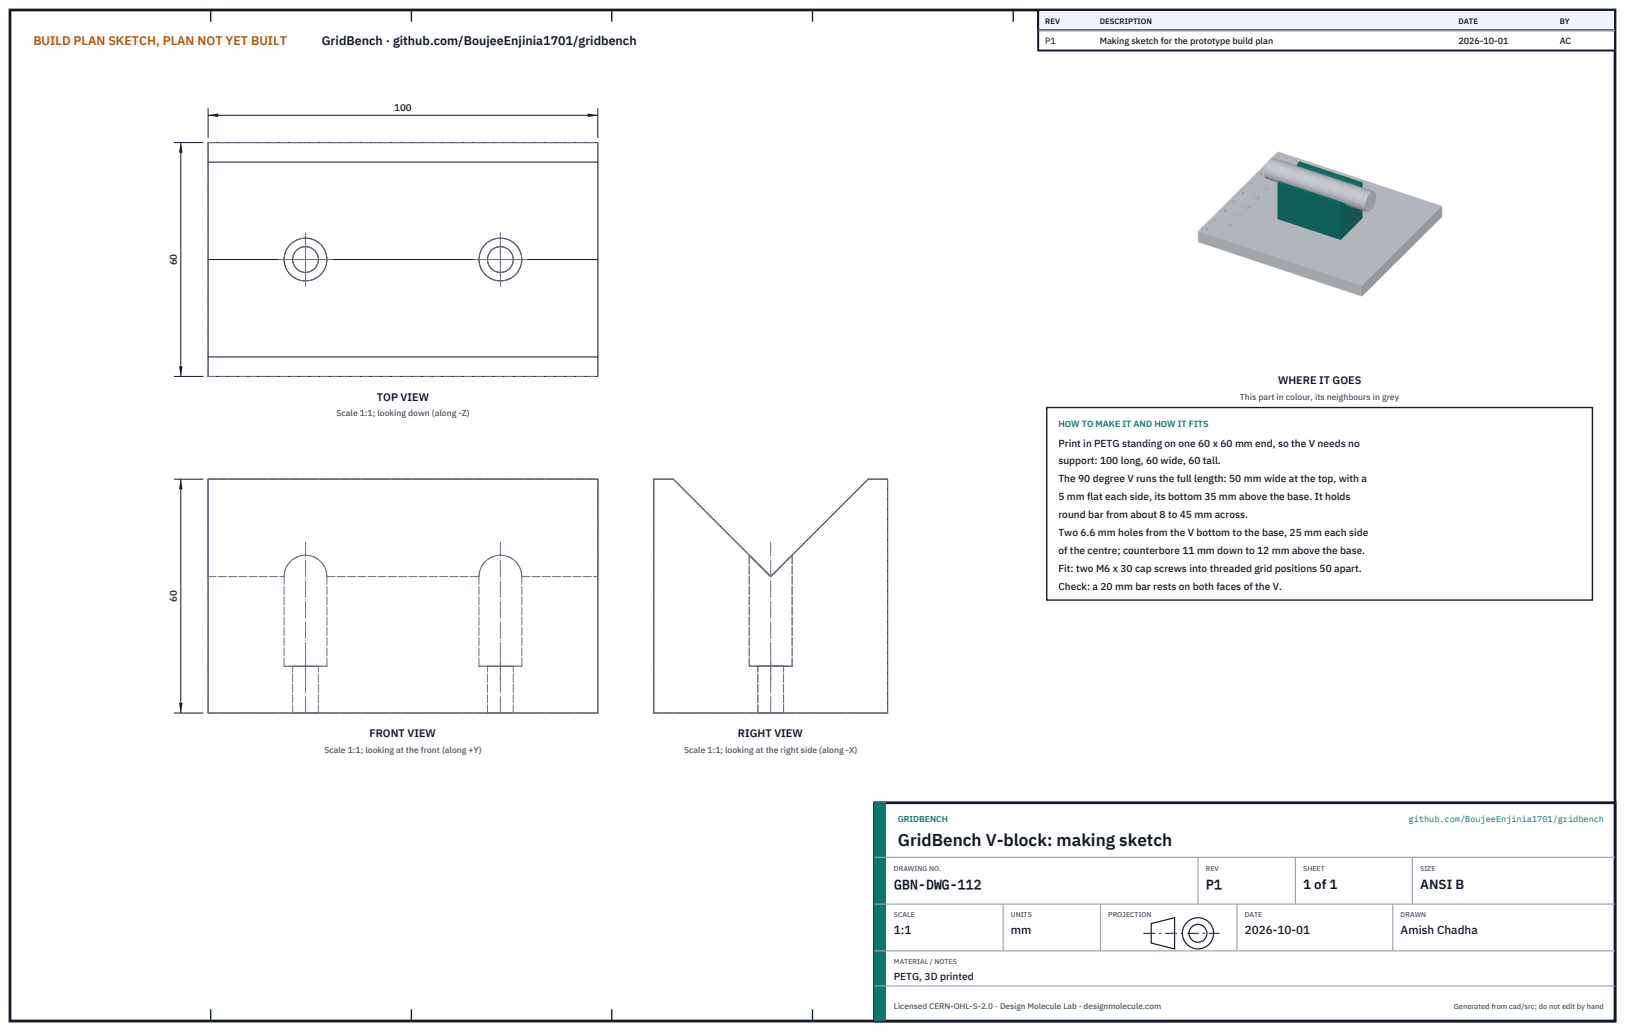
[picture p97: page 1]
BUILD PLAN SKETCH, PLAN NOT YET BUILT; GridBench · github.com/BoujeeEnjinia1701/gridbench; FRONT VIEW; TOP VIEW; RIGHT VIEW; REV; DESCRIPTION; DATE; Making sketch for the prototype build plan; GRIDBENCH; github.com/BoujeeEnjinia1701/gridbench; DRAWING NO. GBN-DWG-112; REV P1; SHEET 1 of 1; SIZE ANSI B; SCALE 1:1; UNITS mm; PROJECTION; DRAWN Amish Chadha; MATERIAL / NOTES PETG, 3D printed; Licensed CERN-OHL-S-2.0 · Design Molecule Lab · designmolecule.com; Generated from cad/src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

WHERE IT GOES

This part in colour, its neighbours in grey

Scale 1:1; looking down (along -Z)

HOW TO MAKE IT AND HOW IT FITS
Print in PETG standing on one 60 x 60 mm end, so the V needs no
support: 100 long, 60 wide, 60 tall.
The 90 degree V runs the full length: 50 mm wide at the top, with a
5 mm flat each side, its bottom 35 mm above the base. It holds
round bar from about 8 to 45 mm across.
Two 6.6 mm holes from the V bottom to the base, 25 mm each side
of the centre; counterbore 11 mm down to 12 mm above the base.
Fit: two M6 x 30 cap screws into threaded grid positions 50 apart.
Check: a 20 mm bar rests on both faces of the V.

Scale 1:1; looking at the front (along +Y)

Scale 1:1; looking at the right side (along -X)

GridBench V-block: making sketch
