BoujeeEnjinia1701/gridbench/cad/drawings/GBN-DWG-113.pdf

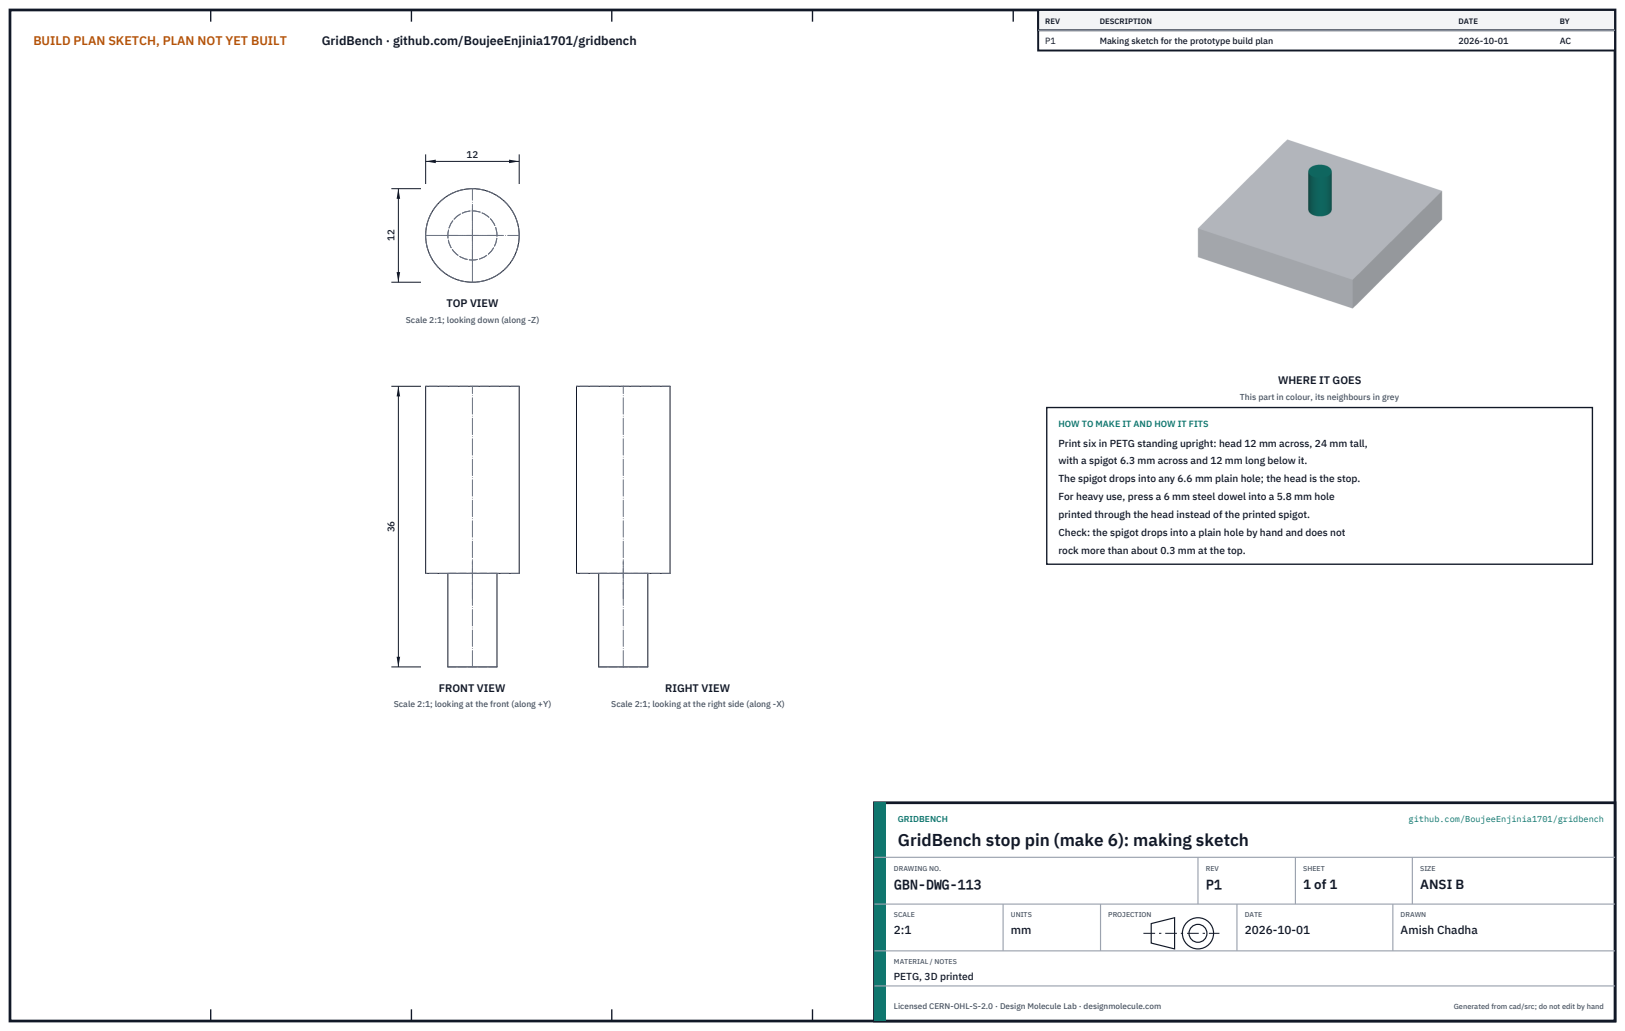
[picture p98: page 1]
BUILD PLAN SKETCH, PLAN NOT YET BUILT; GridBench · github.com/BoujeeEnjinia1701/gridbench; FRONT VIEW; TOP VIEW; RIGHT VIEW; REV; DESCRIPTION; DATE; Making sketch for the prototype build plan; GRIDBENCH; github.com/BoujeeEnjinia1701/gridbench; DRAWING NO. GBN-DWG-113; REV P1; SHEET 1 of 1; SIZE ANSI B; SCALE 2:1; UNITS mm; PROJECTION; DRAWN Amish Chadha; MATERIAL / NOTES PETG, 3D printed; Licensed CERN-OHL-S-2.0 · Design Molecule Lab · designmolecule.com; Generated from cad/src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

Scale 2:1; looking down (along -Z)

WHERE IT GOES

This part in colour, its neighbours in grey

HOW TO MAKE IT AND HOW IT FITS
Print six in PETG standing upright: head 12 mm across, 24 mm tall,
with a spigot 6.3 mm across and 12 mm long below it.
The spigot drops into any 6.6 mm plain hole; the head is the stop.
For heavy use, press a 6 mm steel dowel into a 5.8 mm hole
printed through the head instead of the printed spigot.
Check: the spigot drops into a plain hole by hand and does not
rock more than about 0.3 mm at the top.

Scale 2:1; looking at the front (along +Y)

Scale 2:1; looking at the right side (along -X)

GridBench stop pin (make 6): making sketch
